gfischershaw/1btn/images/1btn_comparison.png

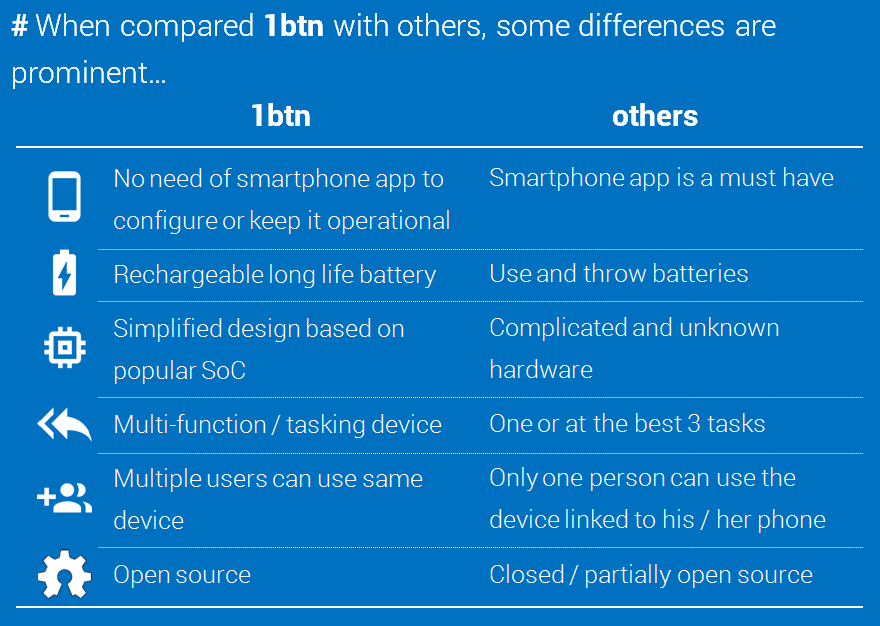
images/1btn_comparison.png
