gfischershaw/1btn/images/1btn_graphic.jpg

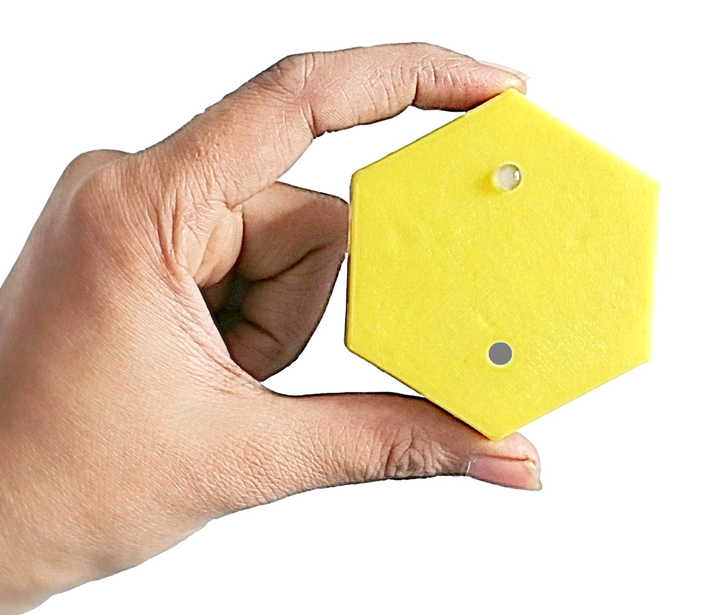
images/1btn_graphic.jpg
