gfischershaw/1btn/images/1btn_pos1.jpg

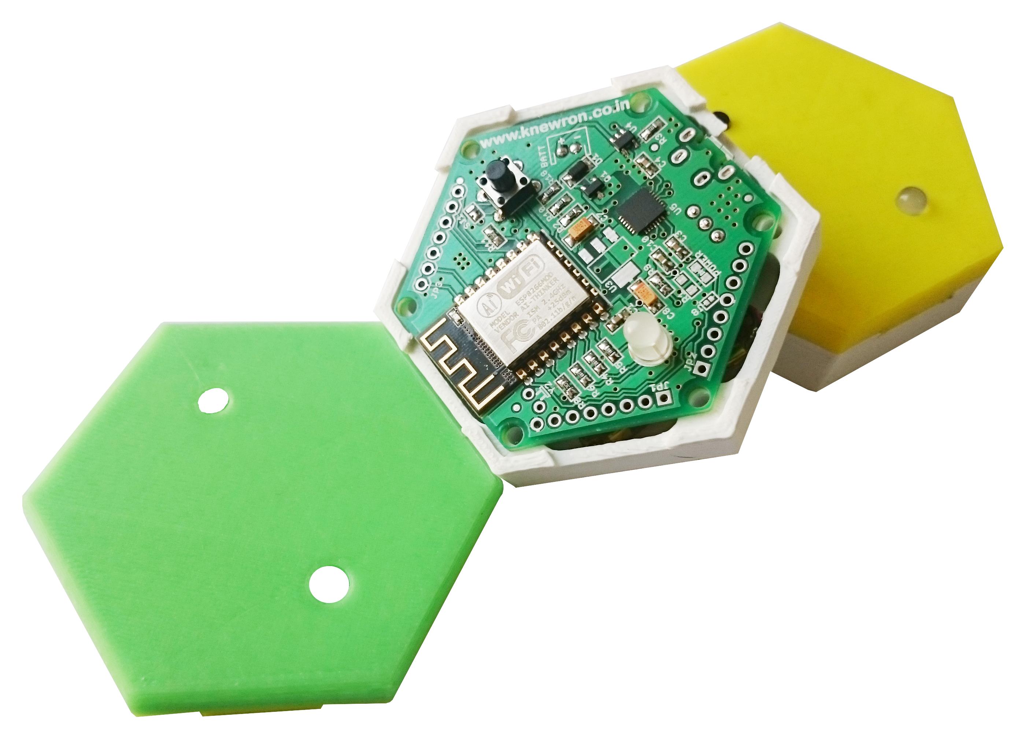
images/1btn_pos1.jpg
