gfischershaw/1btn/images/1btn_pos3.png

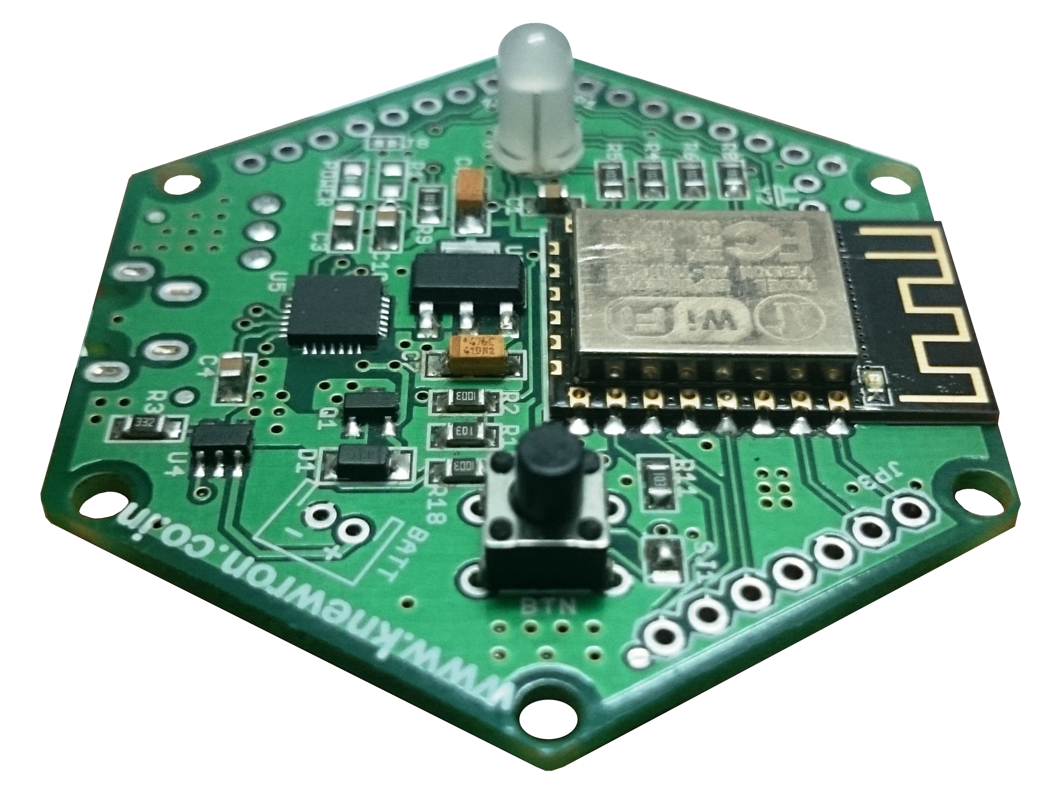
images/1btn_pos3.png
