gfischershaw/1btn/images/1btn_working.png

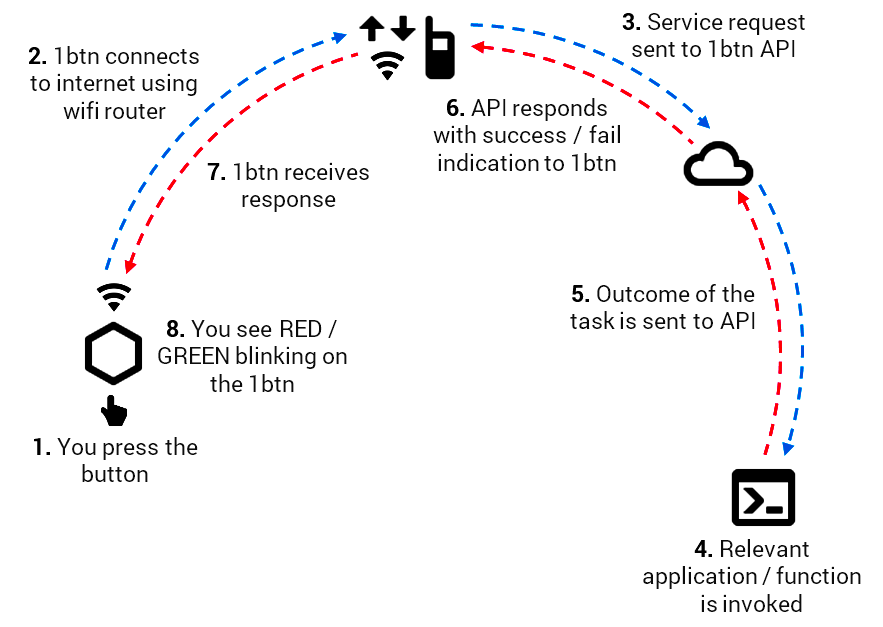
images/1btn_working.png
