gfischershaw/1btn/images/IMG_20151105_214545.jpg

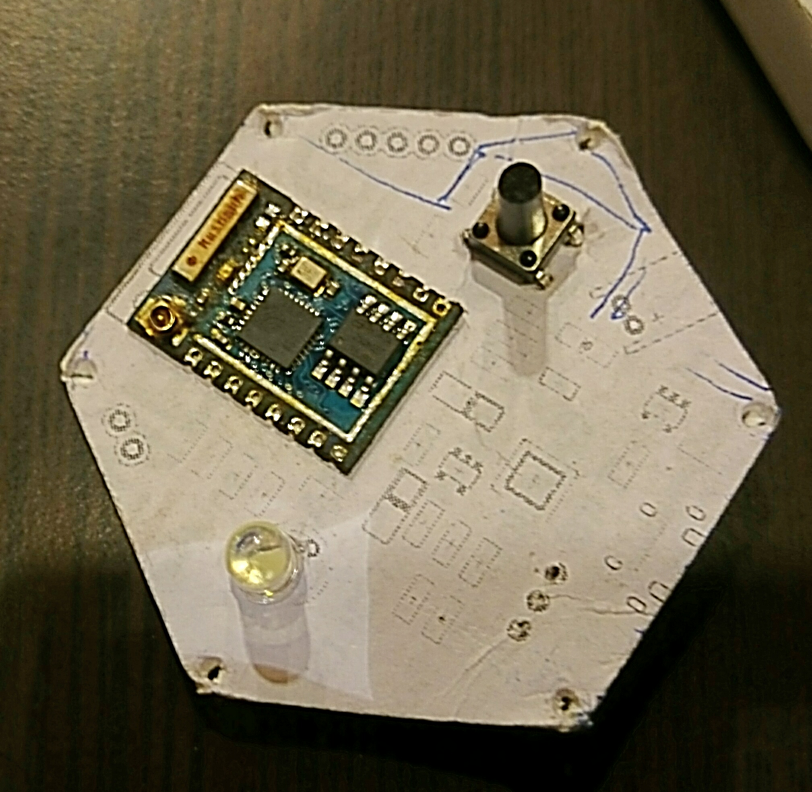
images/IMG_20151105_214545.jpg
