gfischershaw/1btn/mechanical/render v1/2-green_blue.jpg

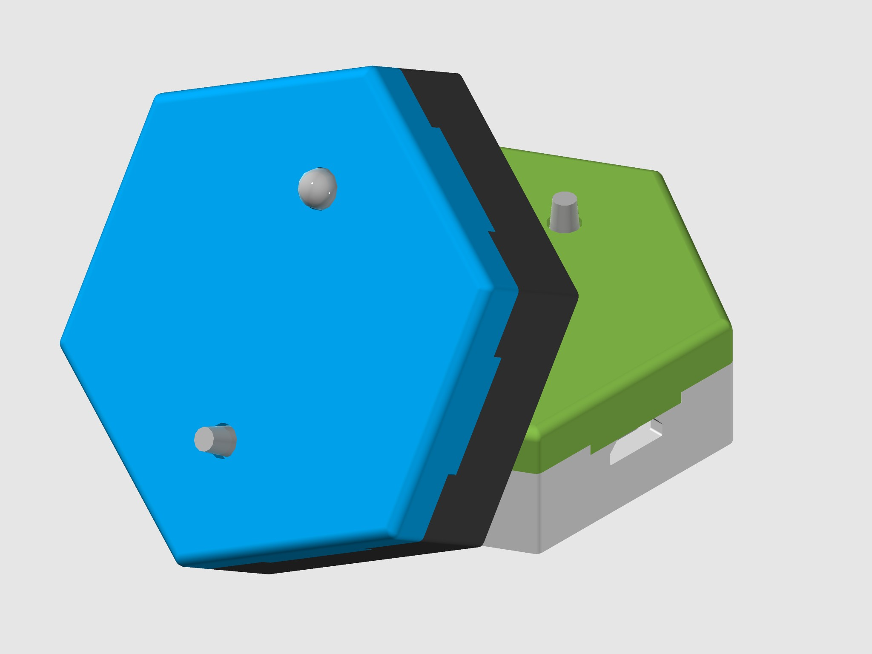
mechanical/render v1/2-green_blue.jpg
