gfischershaw/1btn/mechanical/render v1/blue_black.jpeg

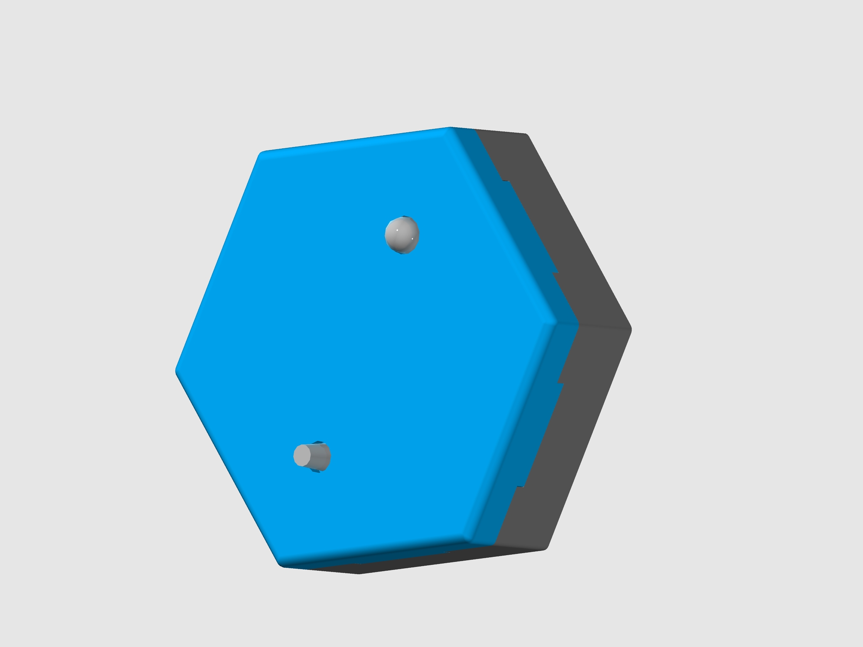
mechanical/render v1/blue_black.jpeg
