gfischershaw/1btn/mechanical/render v1/green_black.jpeg

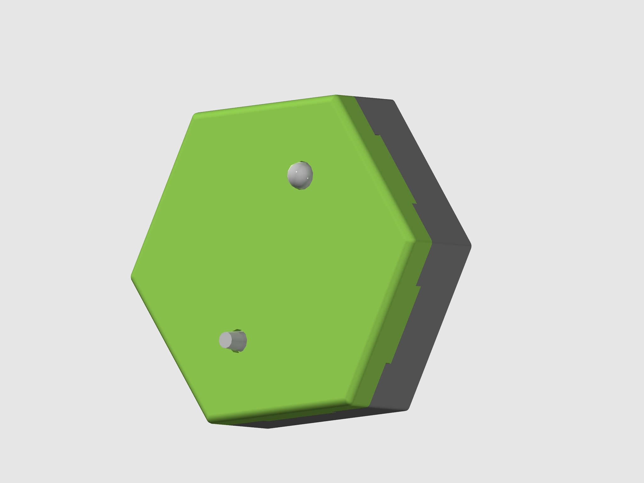
mechanical/render v1/green_black.jpeg
