gfischershaw/1btn/mechanical/render v1/red_black.jpeg

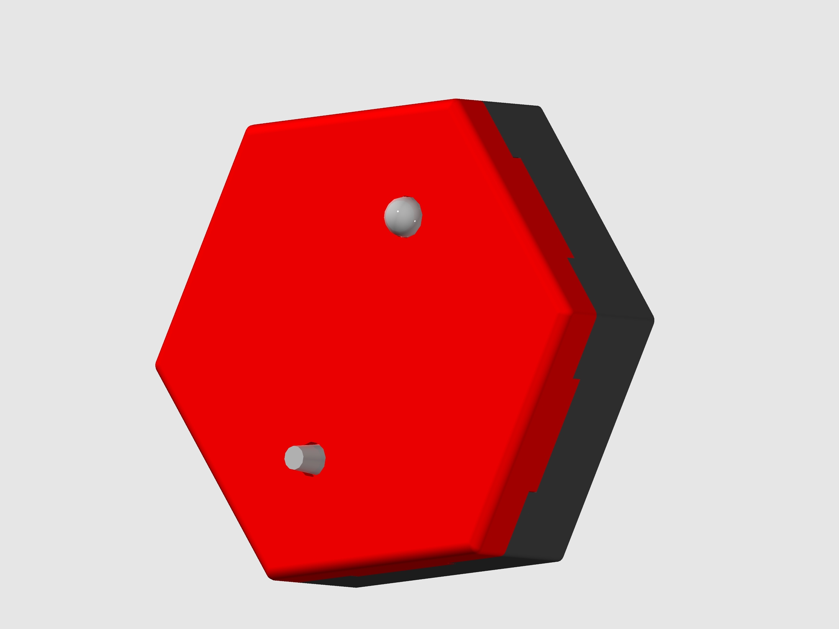
mechanical/render v1/red_black.jpeg
