gfischershaw/1btn/pcb/bottom-layout.png

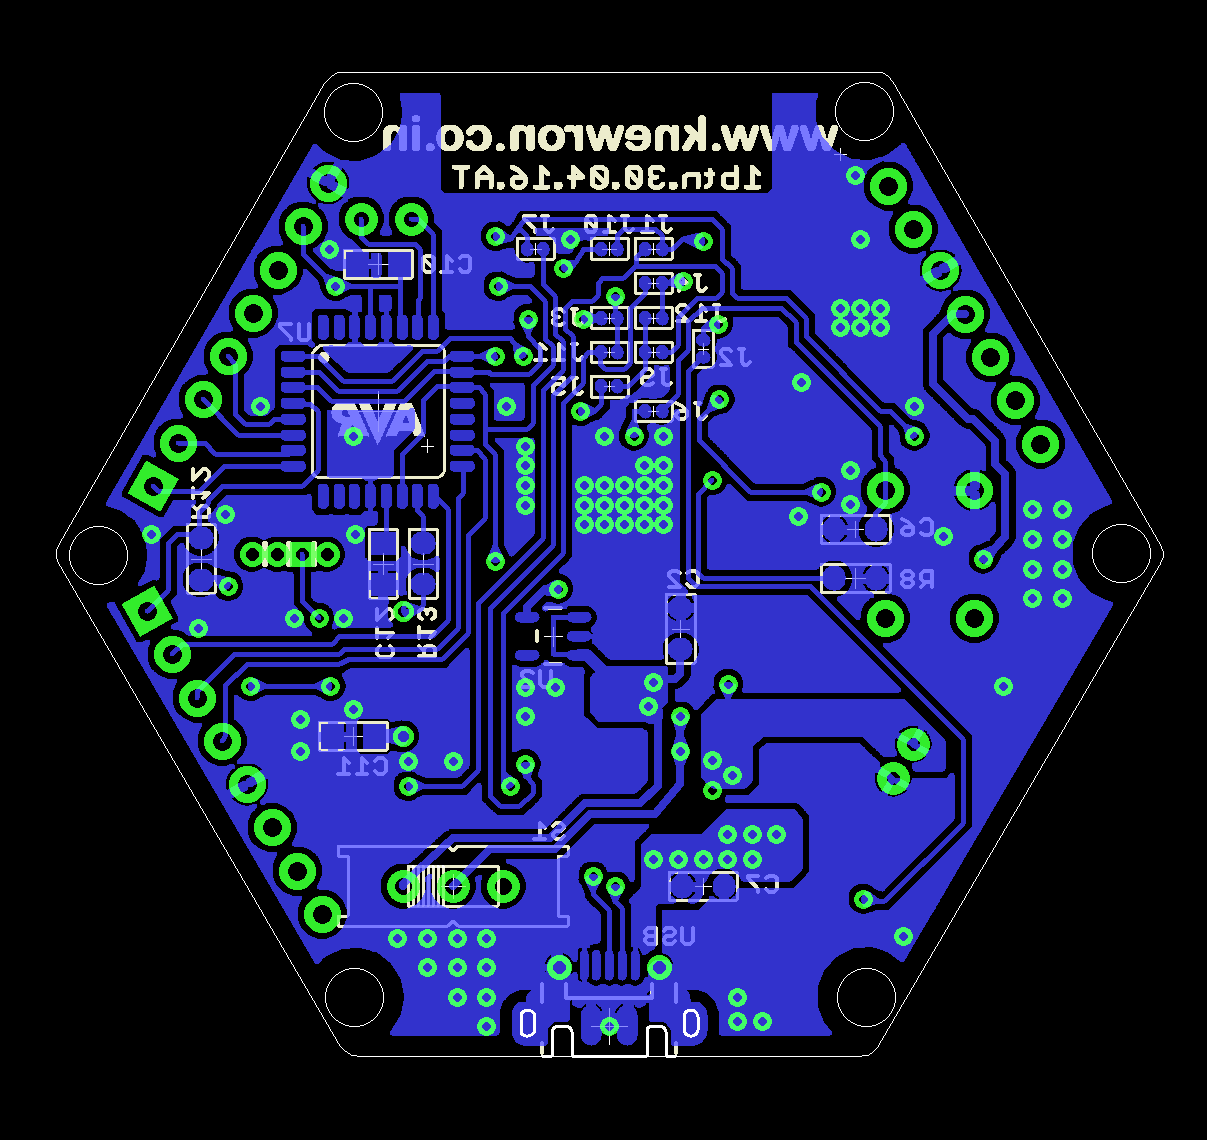
pcb/bottom-layout.png
