gfischershaw/1btn/pcb/schematic.png

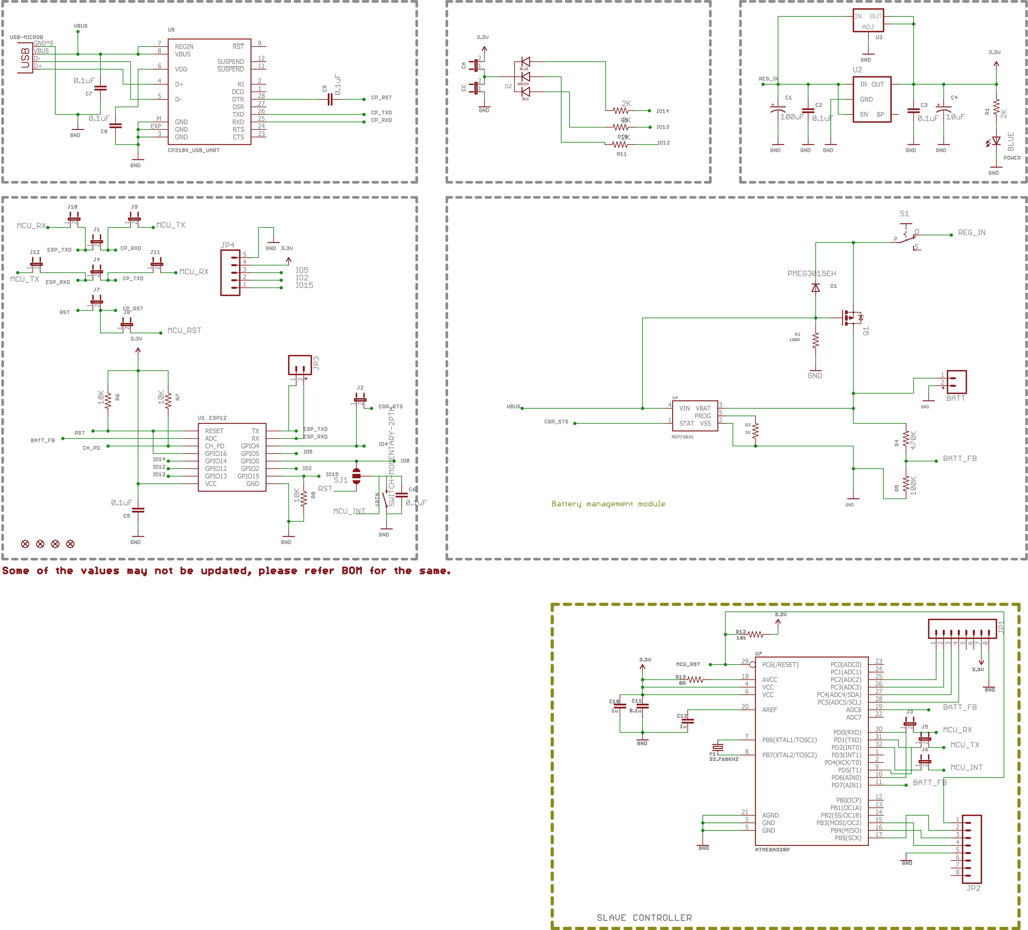
pcb/schematic.png
