gfischershaw/1btn/pcb/top-layout.png

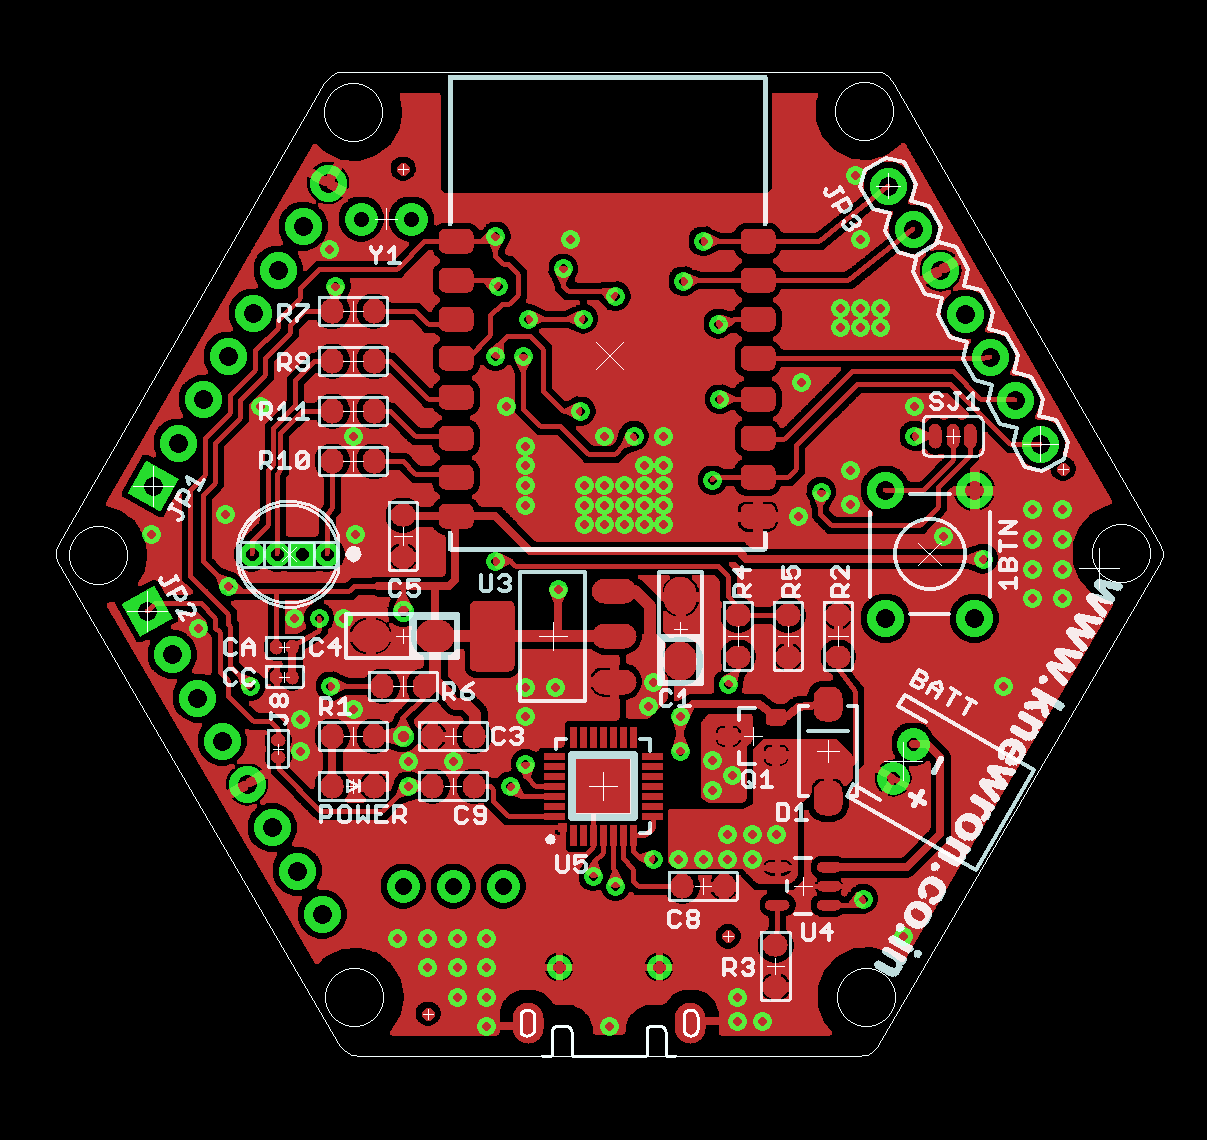
pcb/top-layout.png
