gfischershaw/1btn/use cases and tests/1btn_teardown_and_hardware_hacking/1btn_details.png

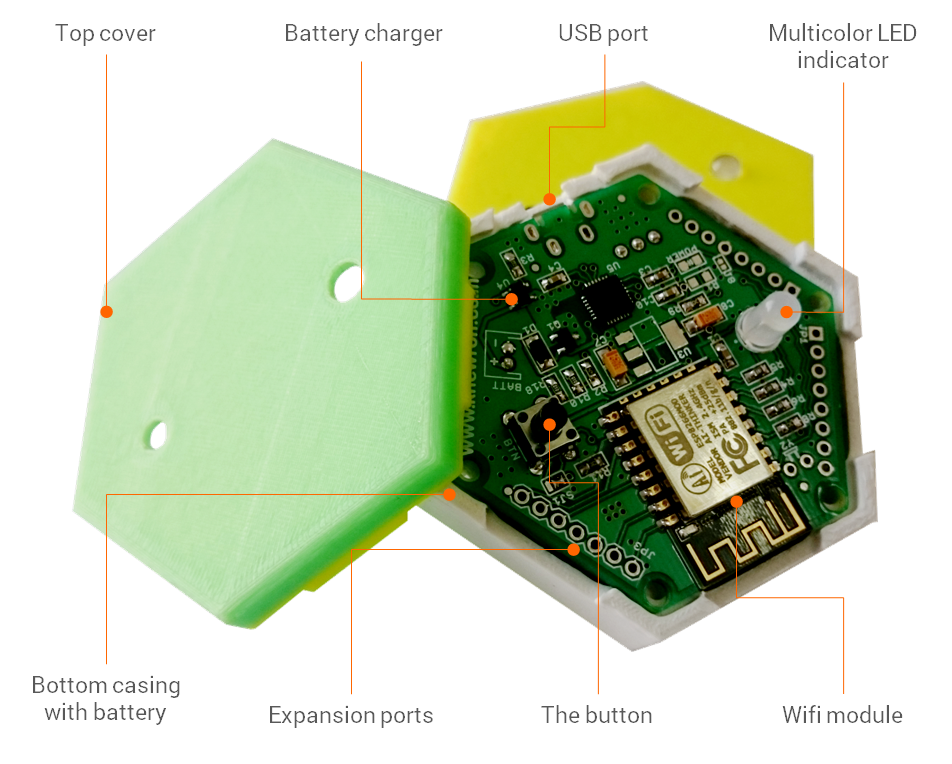
use cases and tests/1btn_teardown_and_hardware_hacking/1btn_details.png
