gfischershaw/1btn/use cases and tests/1btn_teardown_and_hardware_hacking/pcba_top_2.png

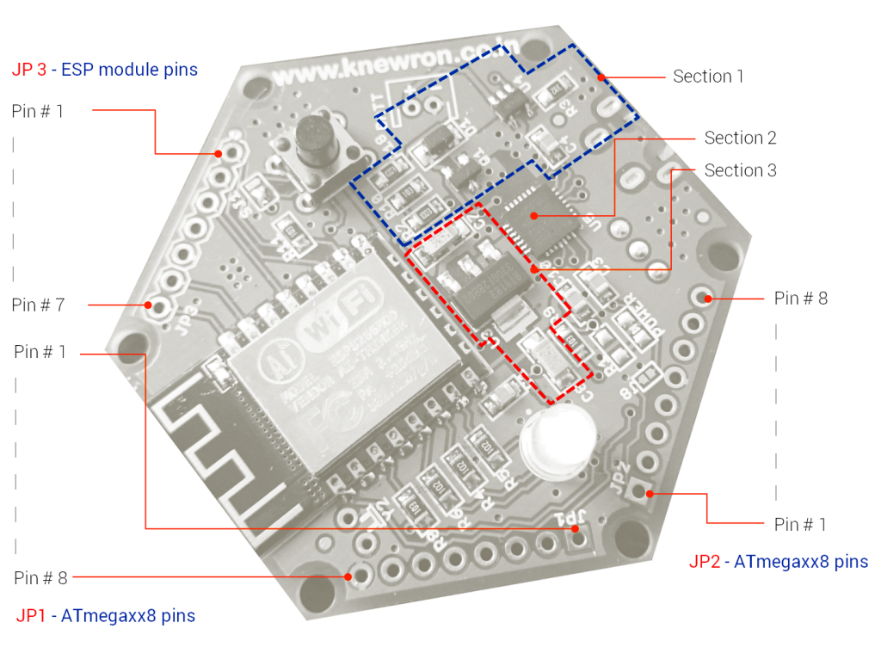
use cases and tests/1btn_teardown_and_hardware_hacking/pcba_top_2.png
