gfischershaw/1btn/use cases and tests/1btn_teardown_and_hardware_hacking/top_casing.png

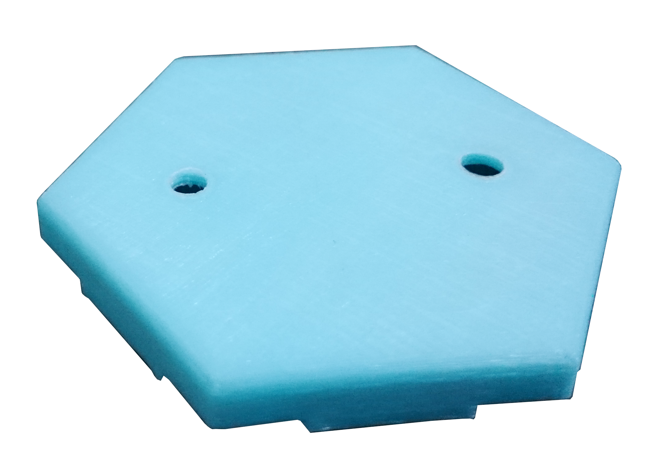
use cases and tests/1btn_teardown_and_hardware_hacking/top_casing.png
