gfischershaw/1btn/use cases and tests/using_reed_switch_with_1btn/6_installed_hacked_1btn_with_reed_switch_2.jpg

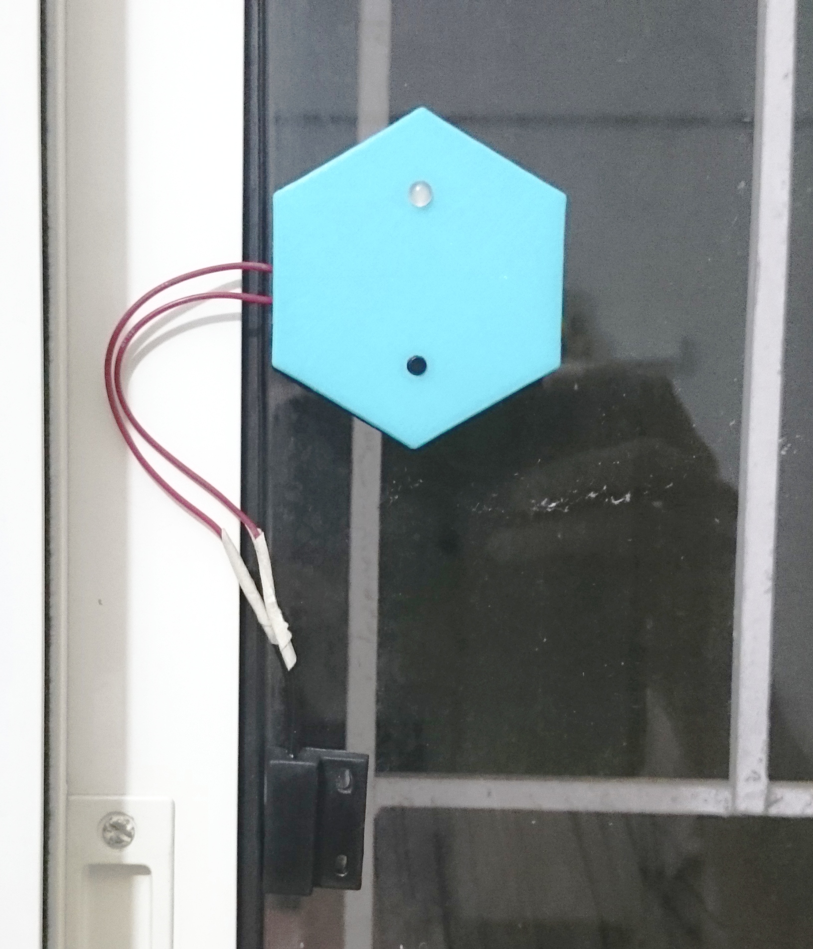
use cases and tests/using_reed_switch_with_1btn/6_installed_hacked_1btn_with_reed_switch_2.jpg
