gfischershaw/1btn/use cases and tests/using_reed_switch_with_1btn/s1_modify_existing_button.png

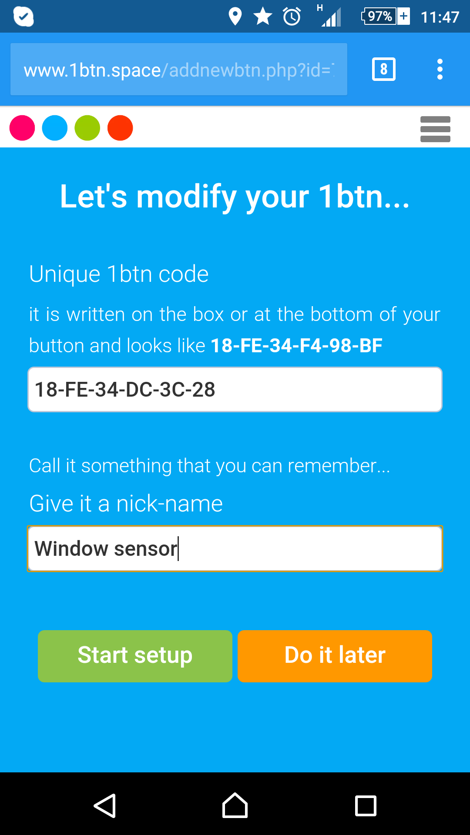
use cases and tests/using_reed_switch_with_1btn/s1_modify_existing_button.png
